beryu/kb-1/img/battery-cover-1.JPG

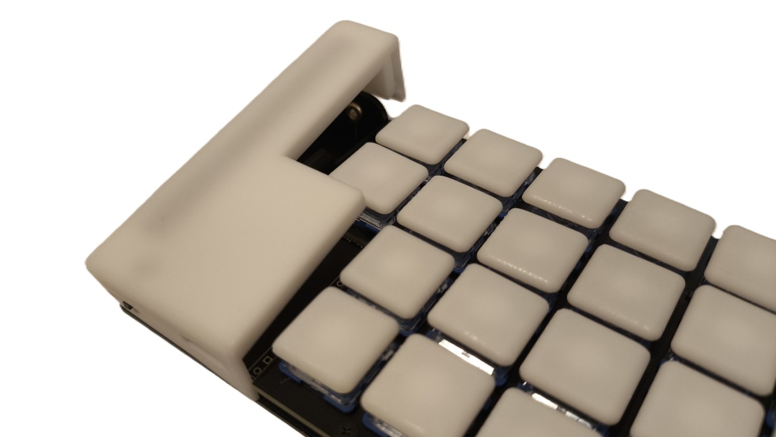
img/battery-cover-1.JPG
