beryu/kb-1/img/battery-cover-2.JPG

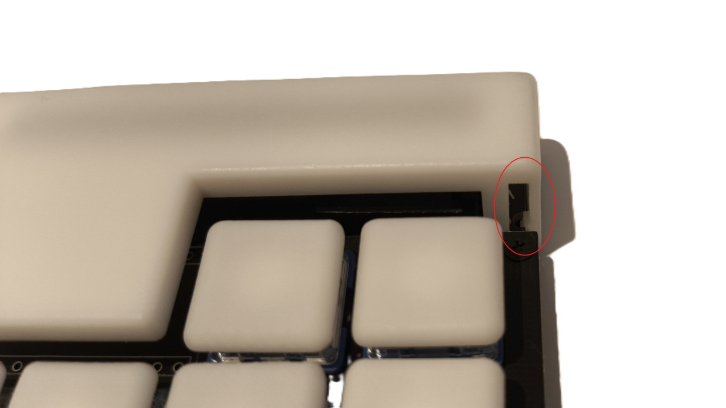
img/battery-cover-2.JPG
