beryu/kb-1/img/led-resistor.JPG

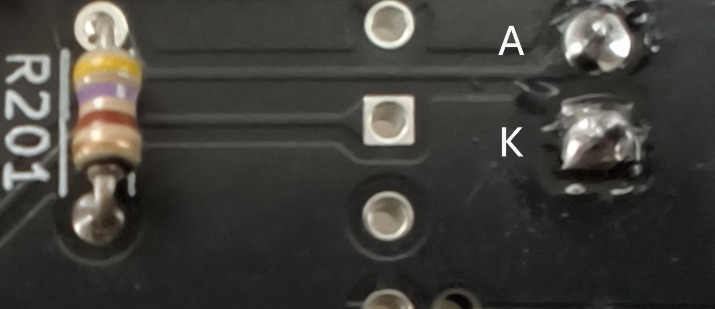
img/led-resistor.JPG
