beryu/kb-1/img/torabo-tsuki-om-s-side.JPG

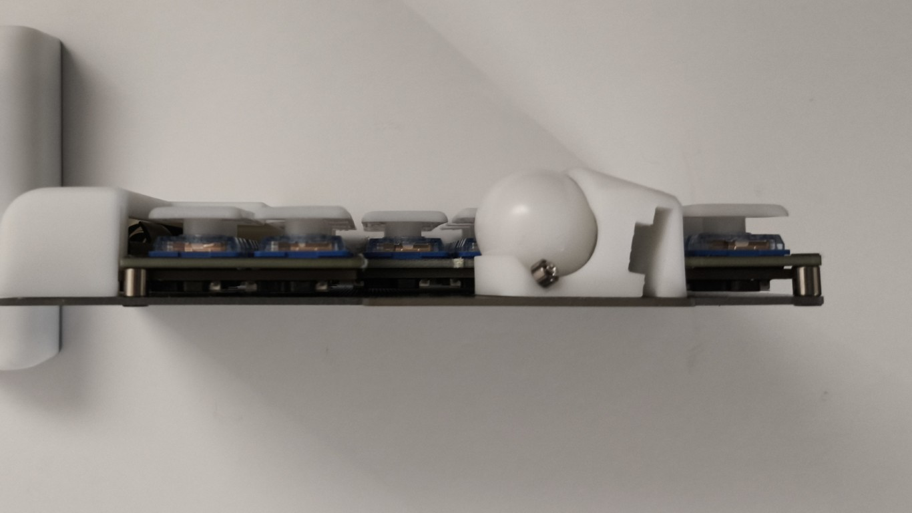
img/torabo-tsuki-om-s-side.JPG
